Redstone1024/Fursuit-CylinderFan/STLs/CylinderFan-Battery-Shell.stl

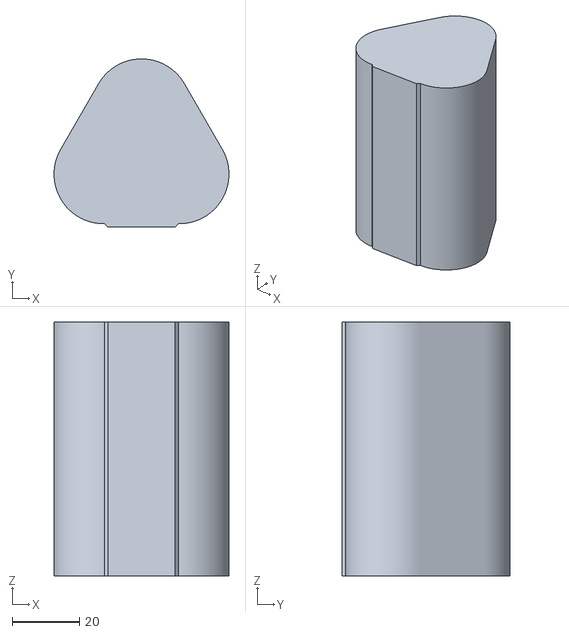
[picture p15: CAD file, 2024-03-23]
STLs/CylinderFan-Battery-Shell.stl
52.0 x 50.0 x 75.5
