Redstone1024/Fursuit-CylinderFan/STLs/CylinderFan-Battery-Seal.stl

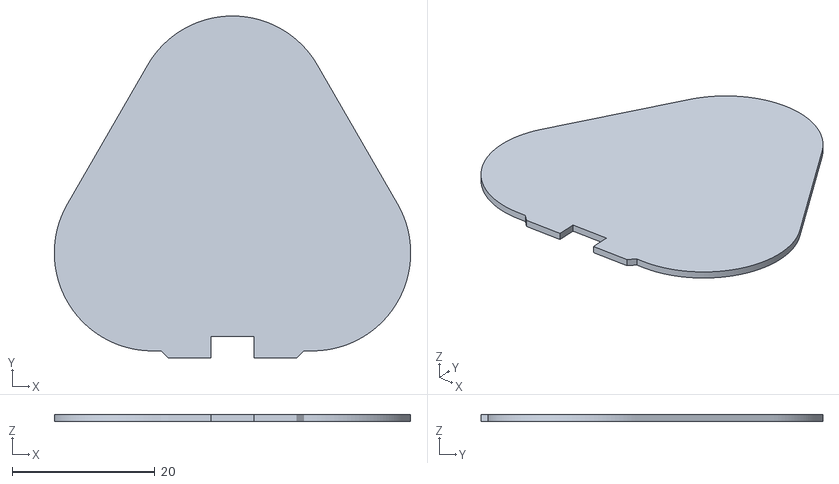
[picture p16: CAD file, 2024-03-23]
STLs/CylinderFan-Battery-Seal.stl
50.0 x 48.0 x 1.00
