Redstone1024/Fursuit-CylinderFan/STLs/CylinderFan-Electronic-Screw.stl

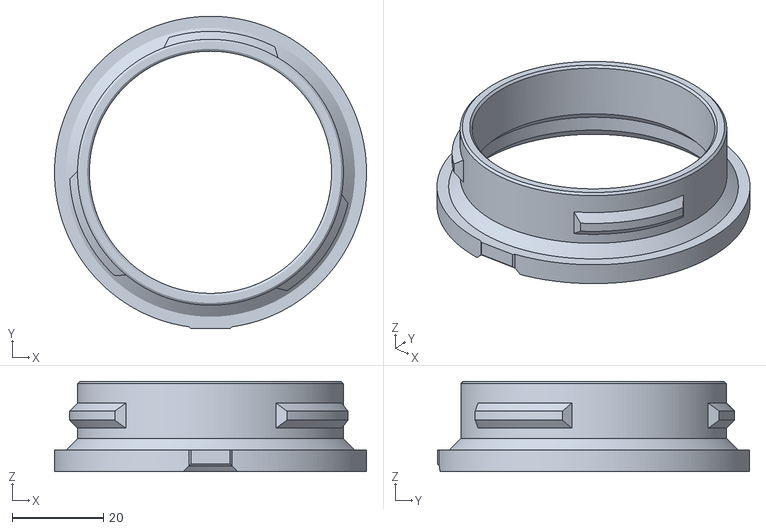
[picture p17: CAD file, 2024-05-31]
STLs/CylinderFan-Electronic-Screw.stl
68.3 x 68.4 x 19.8
